DraFrixUnal/ShinyBike/Visuales/Imagenes/IMG_20230626_190339.jpg

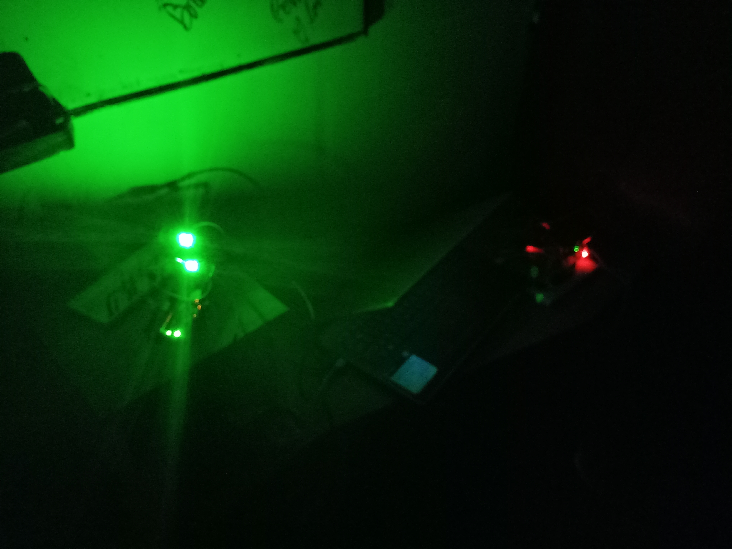
Visuales/Imagenes/IMG_20230626_190339.jpg
