DraFrixUnal/ShinyBike/Visuales/Imagenes/IMG_20230626_190402.jpg

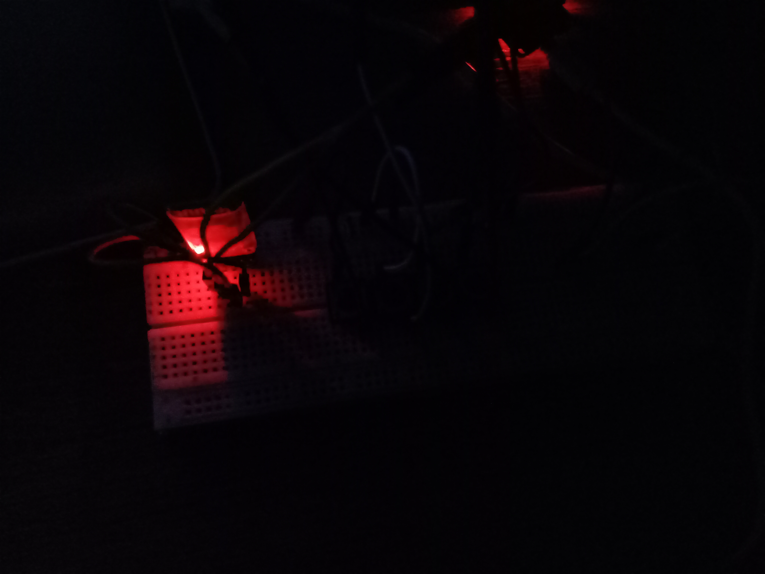
Visuales/Imagenes/IMG_20230626_190402.jpg
