DraFrixUnal/ShinyBike/Kicad-PCB/ControlRemoto/Trazadospdf/ControlRemoto-F_Cu.pdf

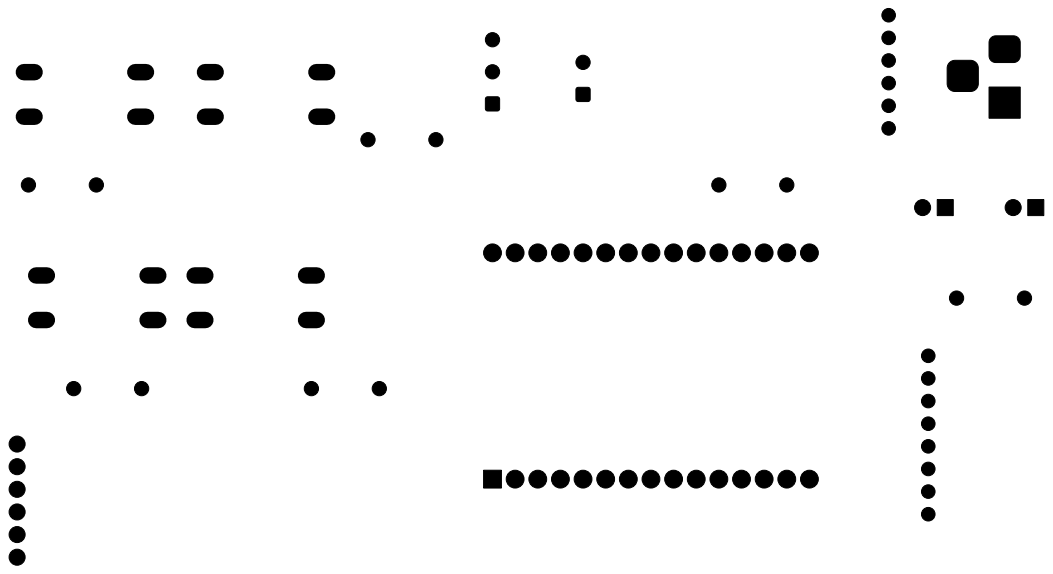
[picture p48: page 1]
