DraFrixUnal/ShinyBike/Kicad-PCB/ControlRemoto/Trazadospdf/ControlRemoto-F_Silkscreen.pdf

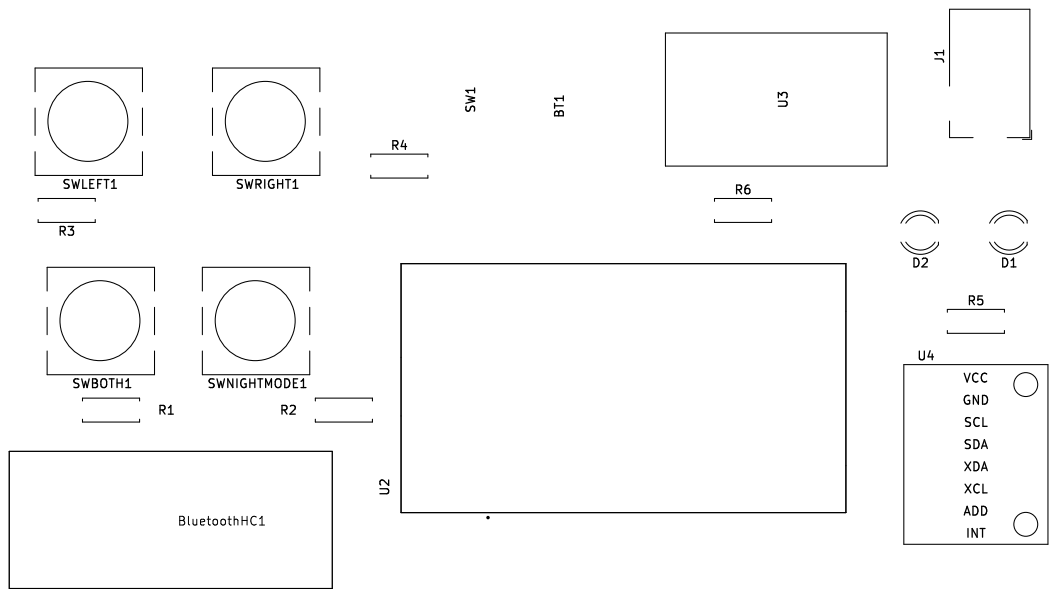
[picture p49: page 1]
