DraFrixUnal/ShinyBike/Kicad-PCB/LUCES/Trazadopdf/LUCES-B_Cu.pdf

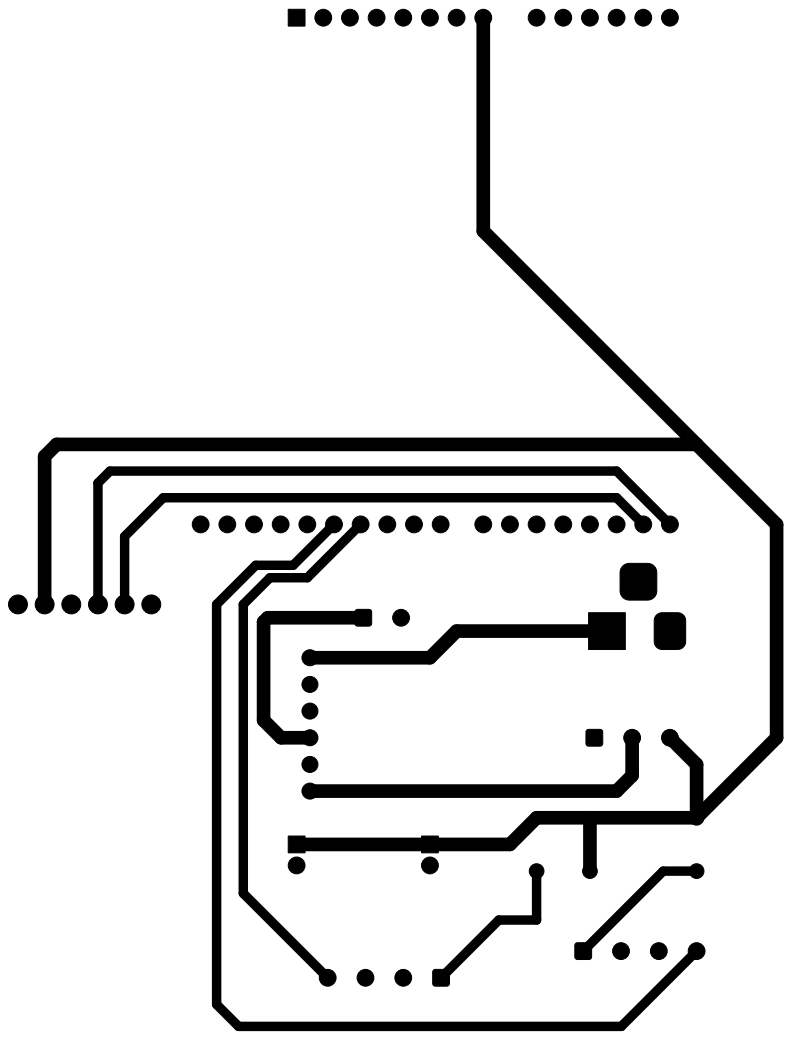
[picture p50: page 1]
