DraFrixUnal/ShinyBike/Kicad-PCB/LUCES/Trazadopdf/LUCES-B_Mask.pdf

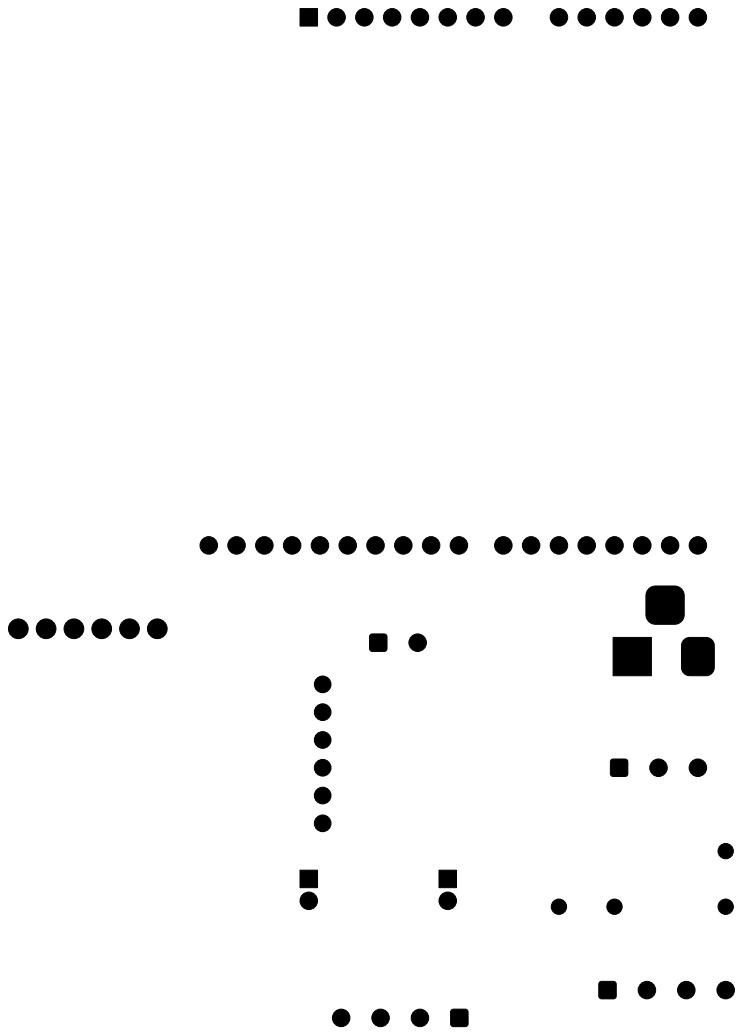
[picture p51: page 1]
