DraFrixUnal/ShinyBike/Kicad-PCB/LUCES/Trazadopdf/LUCES-F_Cu.pdf

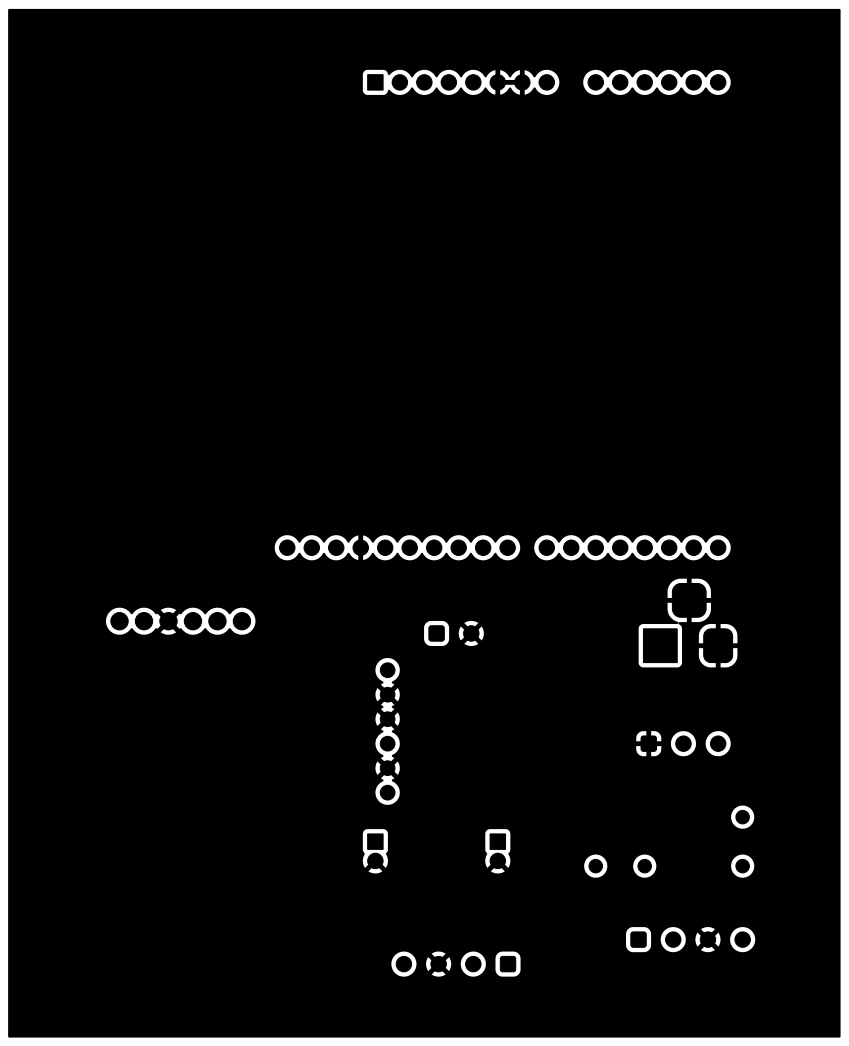
[picture p52: page 1]
