DraFrixUnal/ShinyBike/Kicad-PCB/LUCES/Trazadopdf/LUCES-F_Silkscreen.pdf

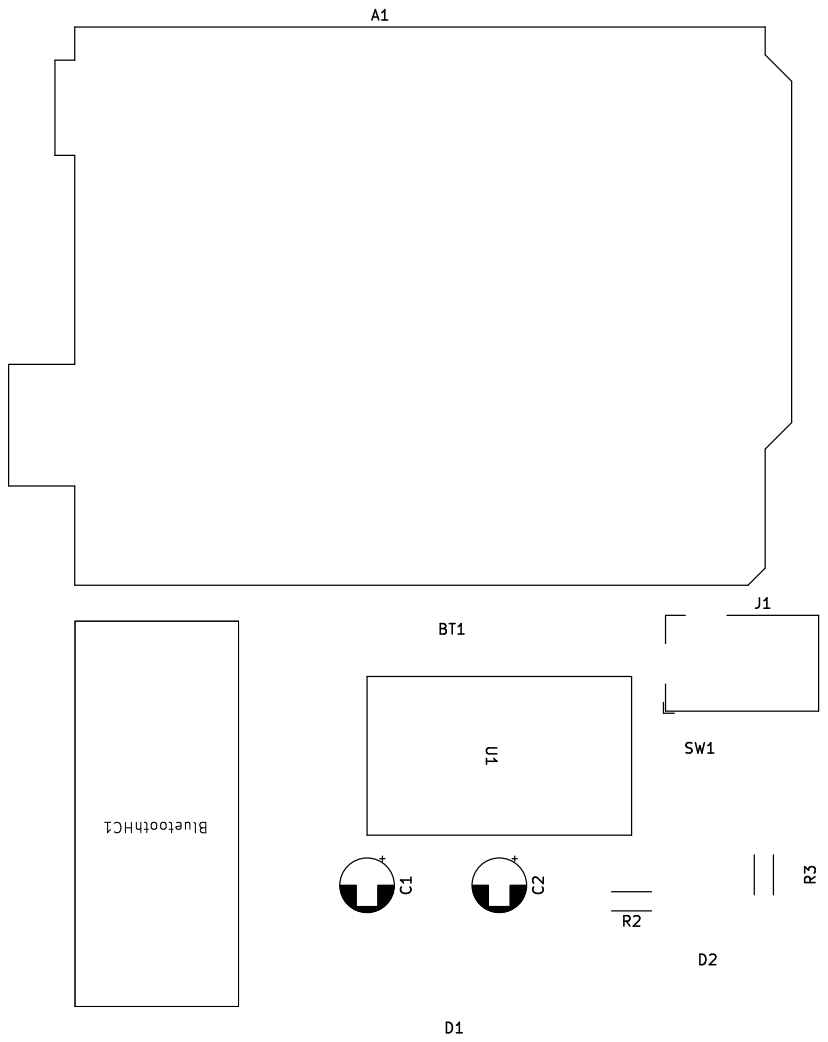
[picture p53: page 1]
